TeamScheire/familiekiosk/testcode/buttonpress/buttonpresstest.py

# -*- coding: utf-8 -*-
"""
Created on Sun May 27 12:14:12 2018

@author: benny
"""

# you need: https://pypi.org/project/RPi.GPIO/ 
# install via: sudo apt-get install python-rpi.gpio python3-rpi.gpio
import RPi.GPIO as GPIO

import time

GPIO.setmode(GPIO.BCM)

#use pin 18 to query the pushbutton
GPIO.setup(18, GPIO.IN, pull_up_down=GPIO.PUD_UP)
#use pin 24 as output for BUZZER
BUZZERPIN = 24
GPIO.setup(BUZZERPIN, GPIO.OUT)

while True:
    input_state = GPIO.input(18)
    if input_state == False:
        print('Button Pressed')
        #buzzer on
        GPIO.output(BUZZERPIN, GPIO.LOW)
        time.sleep(0.2)        
    else:
        GPIO.output(BUZZERPIN, GPIO.HIGH)
        time.sleep(0.2)
        
